BURNTcookiekoki/Guitar-Effects/Photos/Breadboard1.png

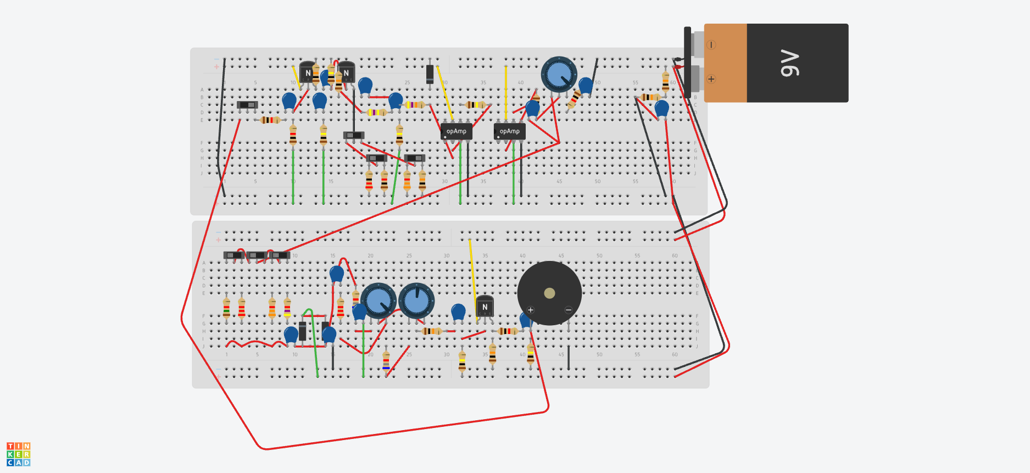
Photos/Breadboard1.png
