BURNTcookiekoki/Guitar-Effects/Photos/CE2.png

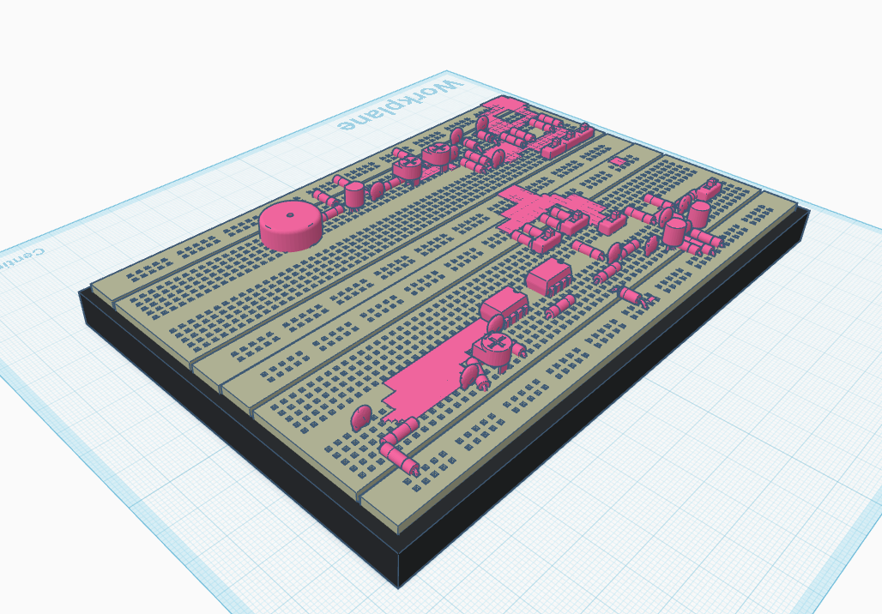
Photos/CE2.png
