BURNTcookiekoki/Guitar-Effects/Photos/p1.png

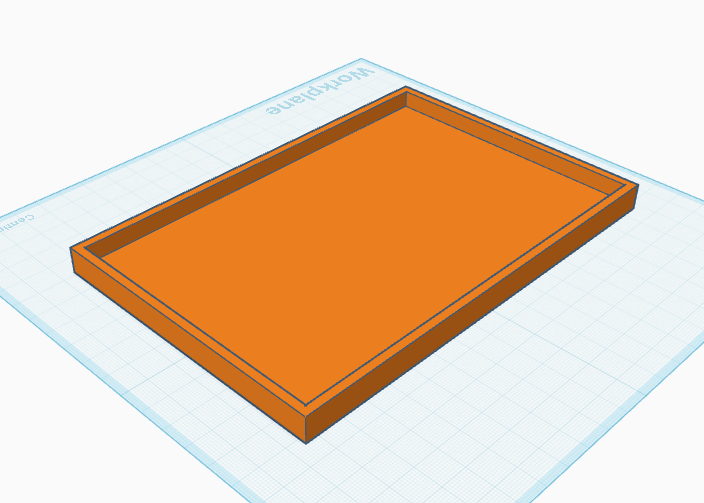
Photos/p1.png
