BURNTcookiekoki/Guitar-Effects/Photos/p2.png

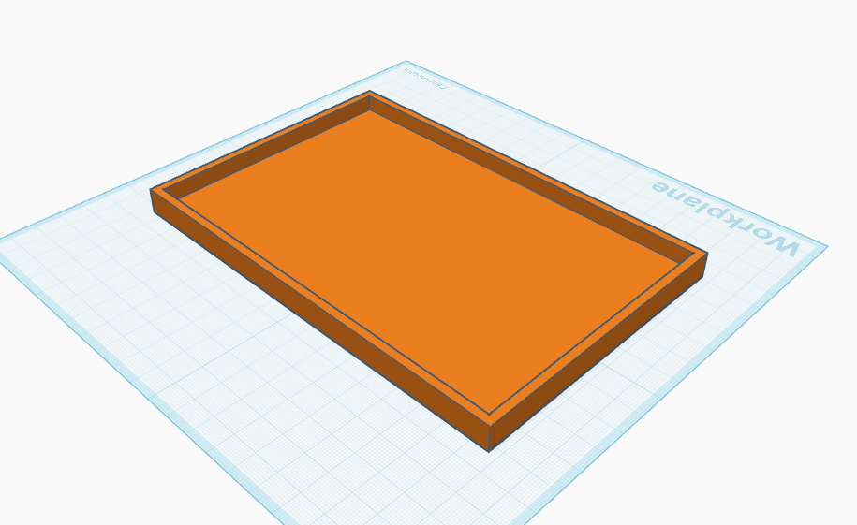
Photos/p2.png
