BURNTcookiekoki/Guitar-Effects/Photos/p3.png

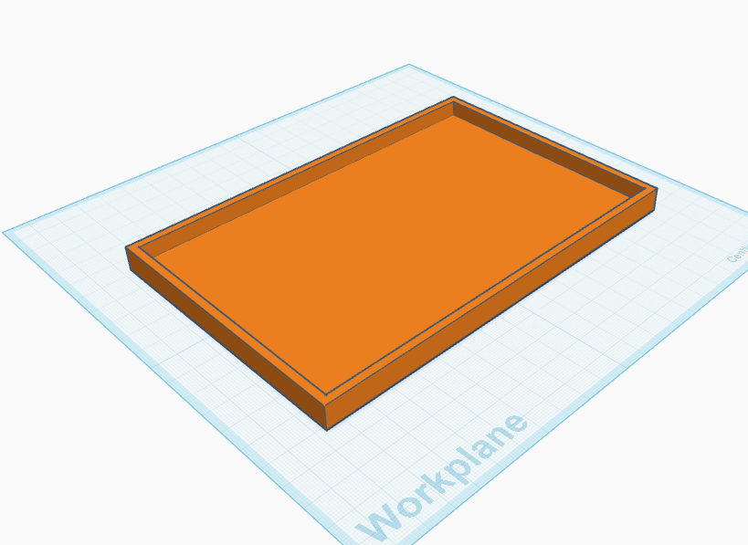
Photos/p3.png
