BURNTcookiekoki/Guitar-Effects/Photos/p4.png

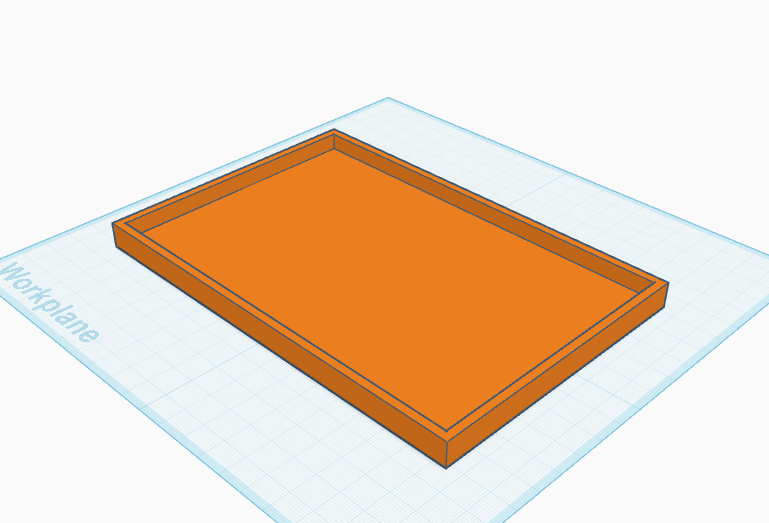
Photos/p4.png
