BURNTcookiekoki/Guitar-Effects/Photos/p5.png

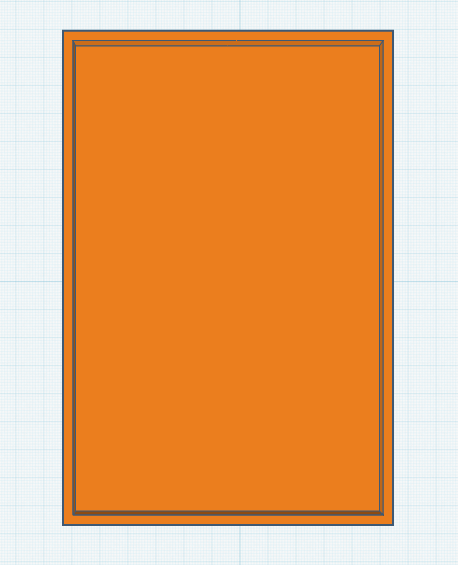
Photos/p5.png
